xpix/XDisPlace/Images/IMG_0286.JPG

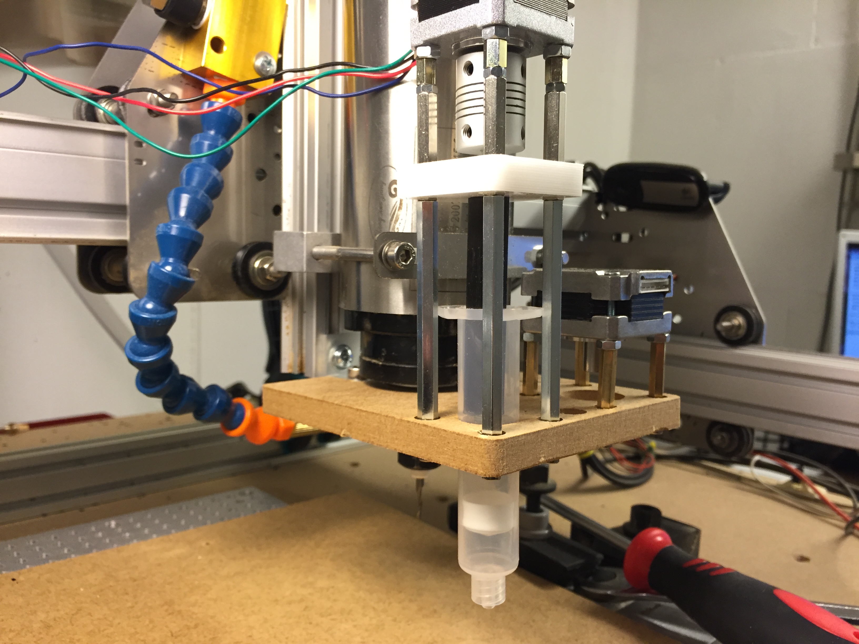
Images/IMG_0286.JPG
