xpix/XDisPlace/Images/IMG_0287.JPG

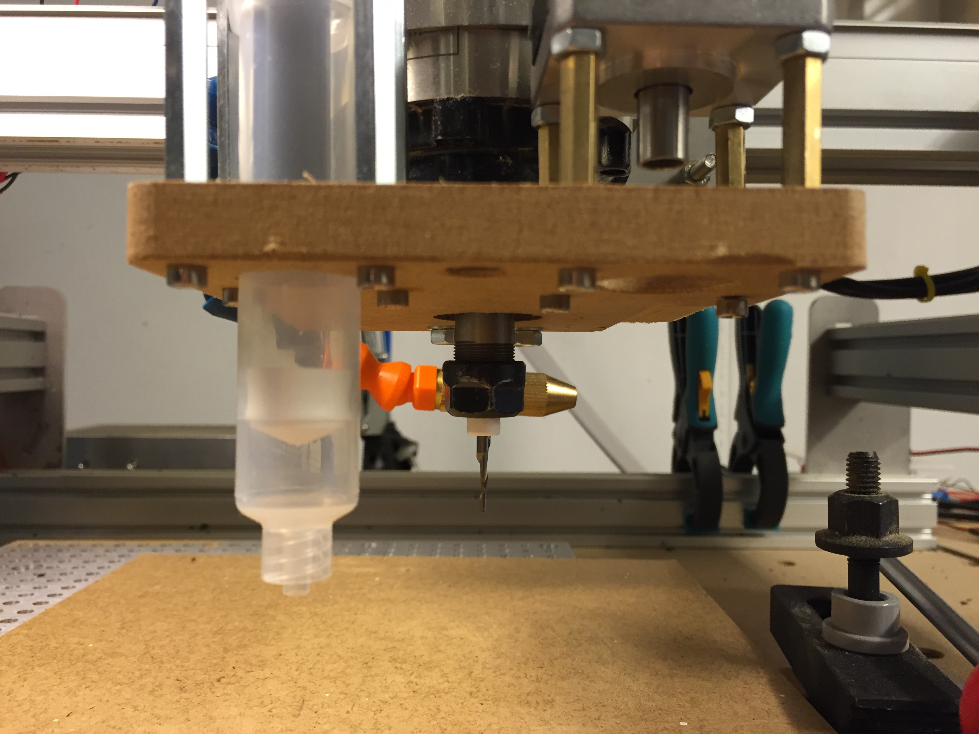
Images/IMG_0287.JPG
